UmutAldioglu67/Smart-Lighting-System-MSP430/hardware/pcb design/WhatsApp Image 2026-06-07 at 13.46.12.jpeg

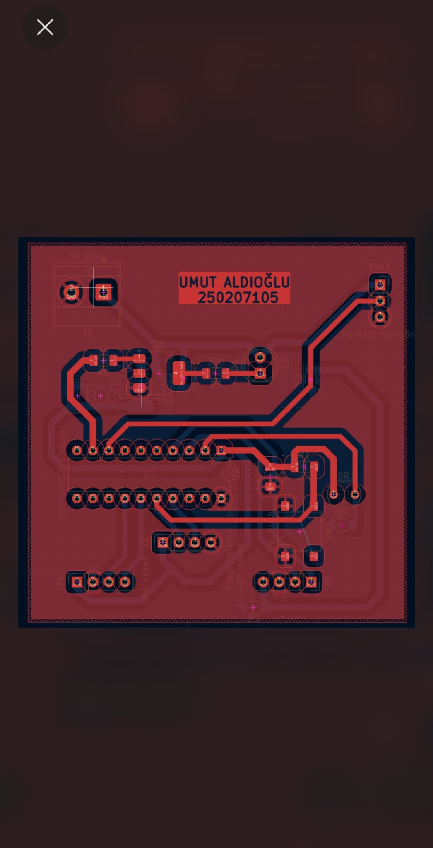
hardware/pcb design/WhatsApp Image 2026-06-07 at 13.46.12.jpeg
