UmutAldioglu67/Smart-Lighting-System-MSP430/hardware/mikro.kicad_sch

## KiCad design hardware/mikro.kicad_sch (2026-07-16)

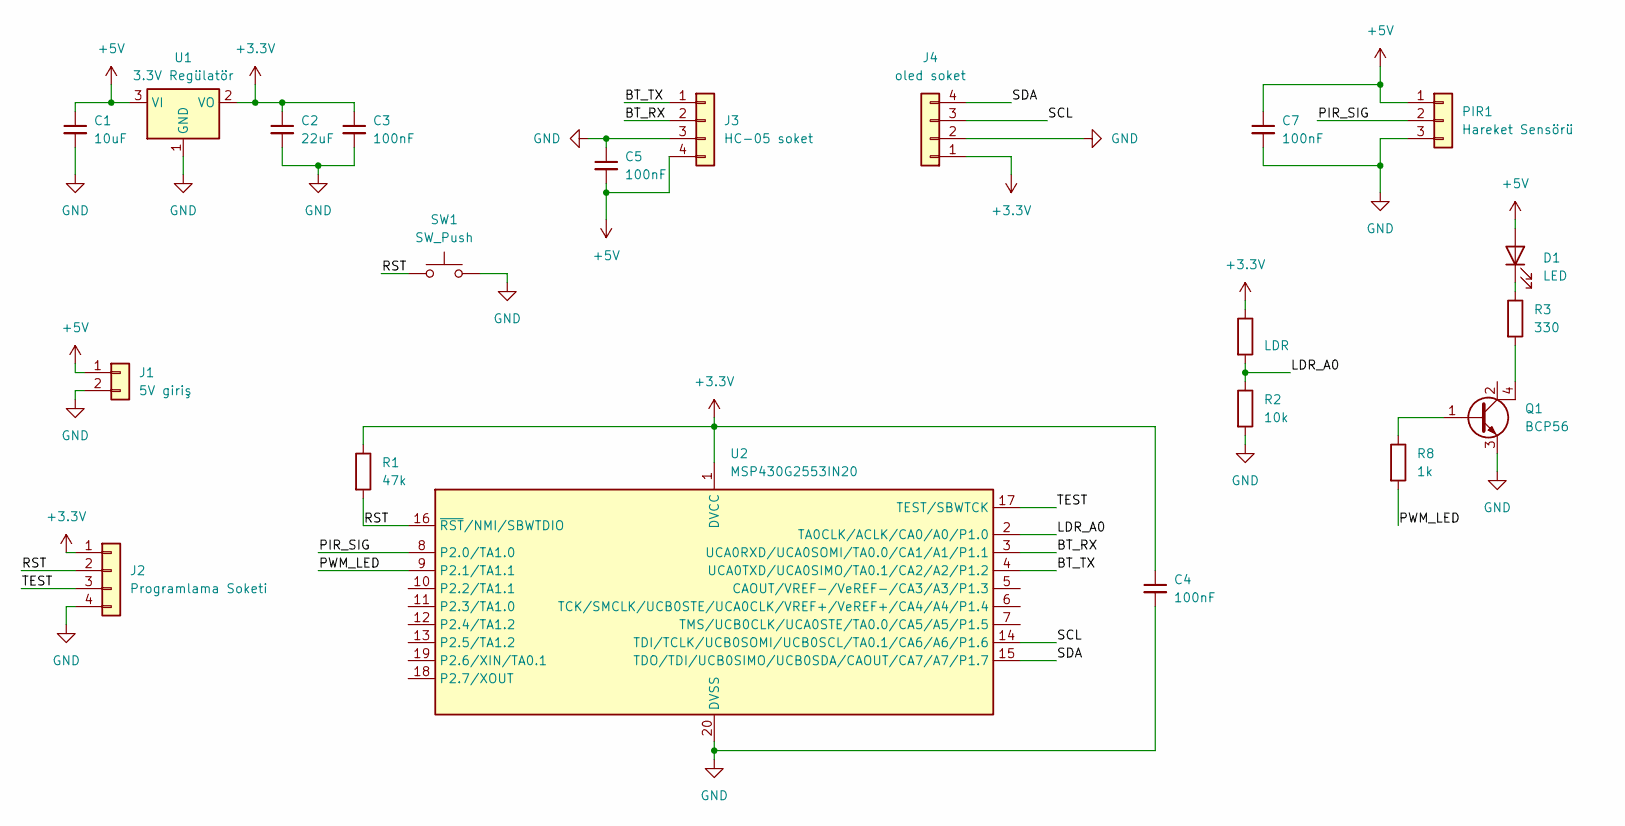
[picture p13: schematic mikro.kicad_sch]

Parts:
C1: 10uF; CP_EIA-3528-21_Kemet-B_HandSolder
C2: 22uF; CP_EIA-3528-21_Kemet-B_HandSolder
C3, C4, C5, C7: 100nF; C_1206_3216Metric_Pad1.33x1.80mm_HandSolder
D1: LED; LED_D5.0mm
J1: 5V giriş; TerminalBlock_Phoenix_MKDS-1,5-2-5.08_1x02_P5.08mm_Horizont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
J2: Programlama Soketi; PinSocket_1x04_P2.54mm_Vertical
J3: HC-05 soket; PinSocket_1x04_P2.54mm_Vertical
J4: oled soket; PinSocket_1x04_P2.54mm_Vertical
LDR1: LDR; R_LDR_5.1x4.3mm_P3.4mm_Vertical
PIR1: Hareket Sensörü; PinSocket_1x03_P2.54mm_Vertical
Q1: BCP56; SOT-223
R1: 47k; R_1206_3216Metric_Pad1.30x1.75mm_HandSolder
R2: 10k; R_1206_3216Metric_Pad1.30x1.75mm_HandSolder
R3: 330; R_1206_3216Metric_Pad1.30x1.75mm_HandSolder
R8: 1k; R_1206_3216Metric_Pad1.30x1.75mm_HandSolder
SW1: SW_Push; SW_SPST_B3S-1000
U1: 3.3V Regülatör; SOT-223-3_TabPin2
U2: MSP430G2553IN20; DIP-20_W7.62mm

Connections:
+3.3V: C2.1, C3.1, C4.1, J2.1, J4.1, LDR1.1, R1.1, U1.2 (VO), U2.1 (DVCC)
+5V: C1.1, C5.2, C7.1, D1.2 (A), J1.1, J3.4, PIR1.1, U1.3 (VI)
BT_RX: J3.2, U2.3 (UCA0RXD/UCA0SOMI/TA0.0/CA1/A1/P1.1)
BT_TX: J3.1, U2.4 (UCA0TXD/UCA0SIMO/TA0.1/CA2/A2/P1.2)
GND: C1.2, C2.2, C3.2, C4.2, C5.1, C7.2, J1.2, J2.4, J3.3, J4.2, PIR1.3, Q1.3 (E), R2.2, SW1.2, U1.1 (GND), U2.20 (DVSS)
LDR_A0: LDR1.2, R2.1, U2.2 (TA0CLK/ACLK/CA0/A0/P1.0)
unnamed: D1.1 (K), R3.1
unnamed: Q1.1 (B), R8.1
unnamed: Q1.4 (C), R3.2
PIR_SIG: PIR1.2, U2.8 (P2.0/TA1.0)
PWM_LED: R8.2, U2.9 (P2.1/TA1.1)
RST: J2.2, R1.2, SW1.1, U2.16 (~RST/NMI/SBWTDIO)
SCL: J4.3, U2.14 (TDI/TCLK/UCB0SOMI/UCB0SCL/TA0.1/CA6/A6/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)
SDA: J4.4, U2.15 (TDO/TDI/UCB0SIMO/UCB0SDA/CAOUT/CA7/A7/P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)
TEST: J2.3, U2.17 (TEST/SBWTCK)
